macsnoeren/hackthebom/hardware/HackTheBom Hardware/HackTheBom Hardware.kicad_sch

## KiCad design hardware/HackTheBom Hardware/HackTheBom Hardware.kicad_sch (2024-09-22)

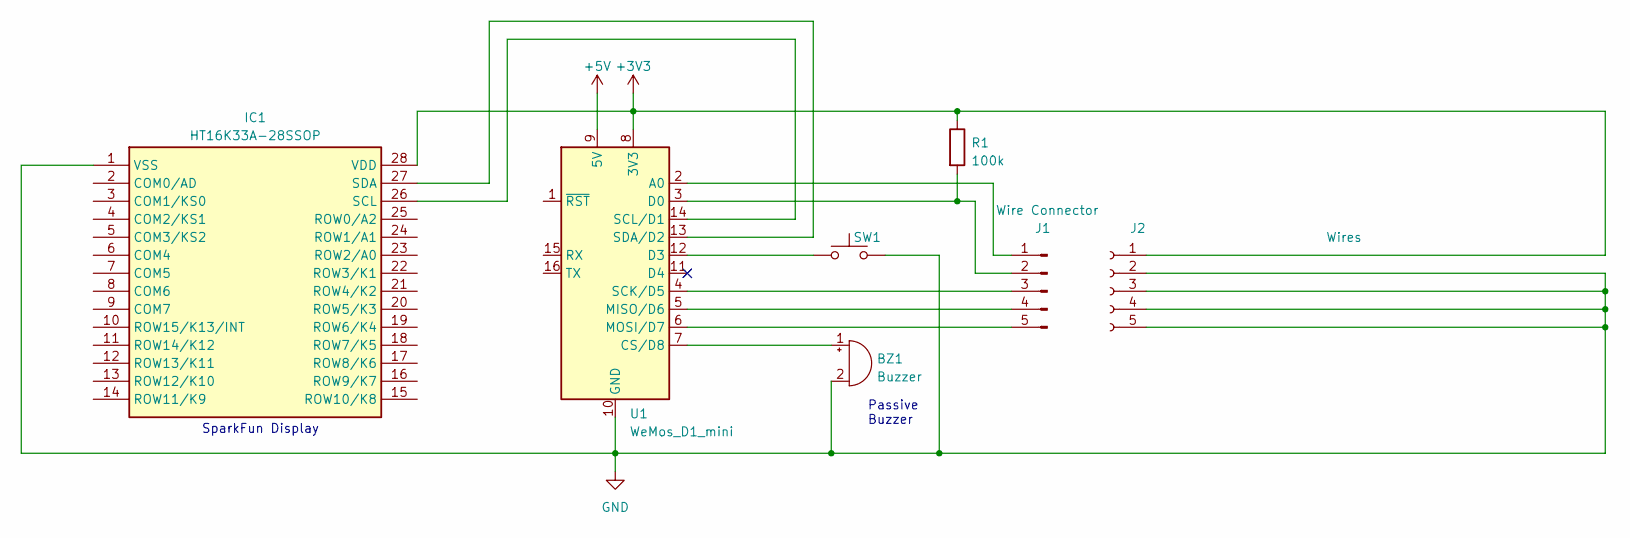
[picture p3: schematic HackTheBom Hardware.kicad_sch]

Parts:
BZ1: Buzzer
IC1: HT16K33A-28SSOP; SOP64P600X175-28N; Manufacturer_Part_Number HT16K33A-28SSOP
J1: Wire Connector
J2: Wires
R1: 100k
SW1: (no value)
U1: WeMos_D1_mini; WEMOS_D1_mini_light

Connections:
+3V3: IC1.28 (VDD), J2.1, R1.1, U1.8 (3V3)
+5V: U1.9 (5V)
GND: BZ1.2 (+), IC1.1 (VSS), J2.2, J2.3, J2.4, J2.5, SW1.3 (B), SW1.4 (B), U1.10 (GND)
unnamed: BZ1.1 (-), U1.7 (CS/D8)
unnamed: IC1.26 (SCL), U1.14 (SCL/D1)
unnamed: IC1.27 (SDA), U1.13 (SDA/D2)
unnamed: J1.1, U1.2 (A0)
unnamed: J1.2, R1.2, U1.3 (D0)
unnamed: J1.3, U1.4 (SCK/D5)
unnamed: J1.4, U1.5 (MISO/D6)
unnamed: J1.5, U1.6 (MOSI/D7)
unnamed: SW1.1 (A), SW1.2 (A), U1.12 (D3)

Notes on the sheet:
Passive Buzzer
SparkFun Display
