macsnoeren/hackthebom/firmware/include/driver.h

#pragma once
/**
 * This file is part of HackTheBom.
 * HackTheBom is free software: you can redistribute it and/or modify it under the
 * terms of the GNU General Public License as published by the Free Software 
 * Foundation, either version 3 of the License, or (at your option) any later 
 * version.
 * 
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
 * @file       : driver.h
 * @author     : Maurice Snoeren (MS)
 * @description: The abstract base class for tasks runned by the SmartSensor board. All tasks should use this class. This file
 *               uses the design approach that starts with interfaces that will be implemented by abstract and concrete classes.
 *               This method provides the interface IDriver.
 * @date       : 27-03-2026
 * @version    : 1.1
 * @updates    : 24-10-2021: Initial code.
 *               27-03-2026 (MS): Improved code and documentation.

 * @todo       : 
 */
#include <inttypes.h>

/* Interface: IDriver
 * The interface that implements the main methods required for a driver.
 */
class IDriver {

public:
    /* The abstract setup method initializes the task. This method should be called once at the startup of the board.
       When the setup is successfull, the method returns 0, otherwise it returns an error number. The error numbers 
       should be documented in the concrete task that implements this setup.
    */
    virtual uint8_t setup() = 0;

    /* The abstract loop method handles the main functionality. This loop method shall not contain any blocking function
       calls. If you require delays, please use timing variable millis. Using this strategy the CPU performance is
       maximized. If successfull the method returns 0, otherwise it returns an error number. The error numbers should be
       documented in the concrete task that implements this loop.
    */
    virtual uint8_t loop(uint64_t millis) = 0;

    /* The abstract reset function resets the task. If successfull the method returns 0, otherwise it returns an error
       number.
    */
    virtual uint8_t reset() = 0;

    /* Put the task to sleep and if possible in low power consumption mode. */
    virtual uint8_t sleep() = 0;

    /* Awake the task so it runs again. */
    virtual uint8_t wakeup() = 0;
};
